simonwa2/F3X-Timing-System/images/base_unit.jpg

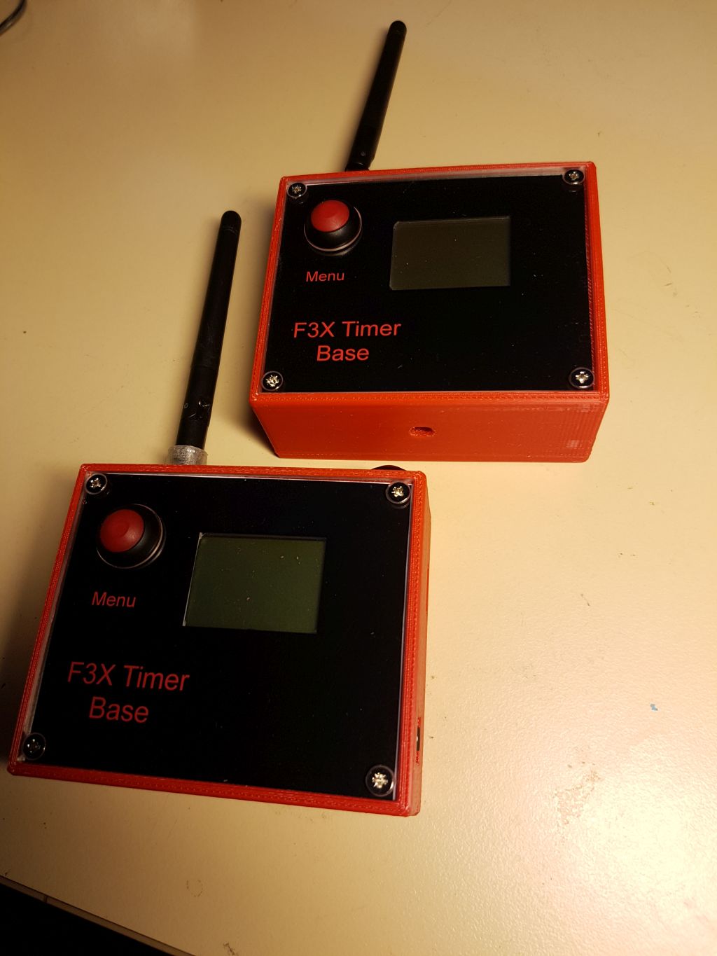
images/base_unit.jpg
