simonwa2/F3X-Timing-System/images/Mini_DIN_6_Connector.jpg

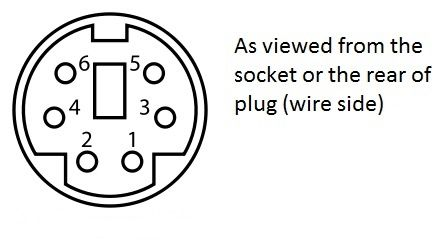
images/Mini_DIN_6_Connector.jpg
