simonwa2/F3X-Timing-System/images/picam_batteries.jpg

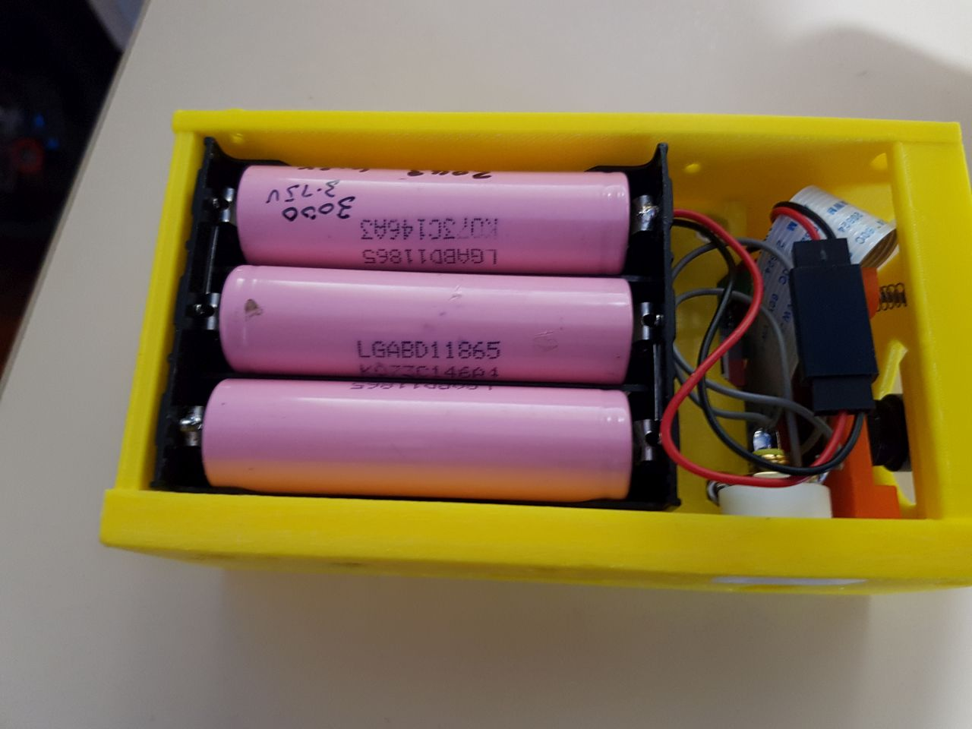
images/picam_batteries.jpg
