simonwa2/F3X-Timing-System/images/picam_bottom.jpg

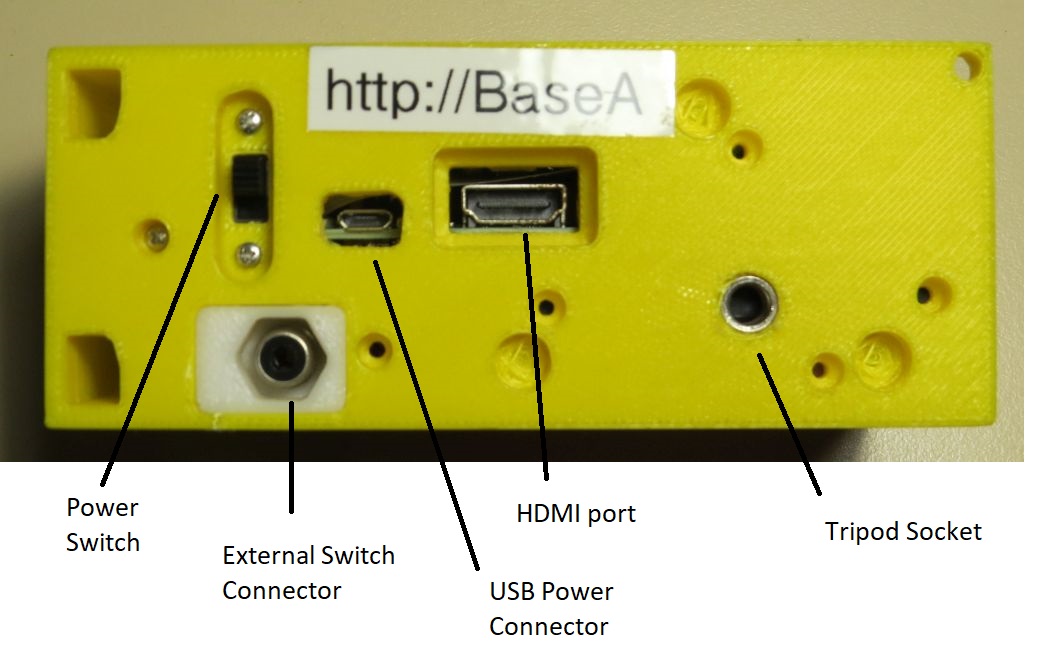
images/picam_bottom.jpg
