simonwa2/F3X-Timing-System/images/picam_preferences.jpg

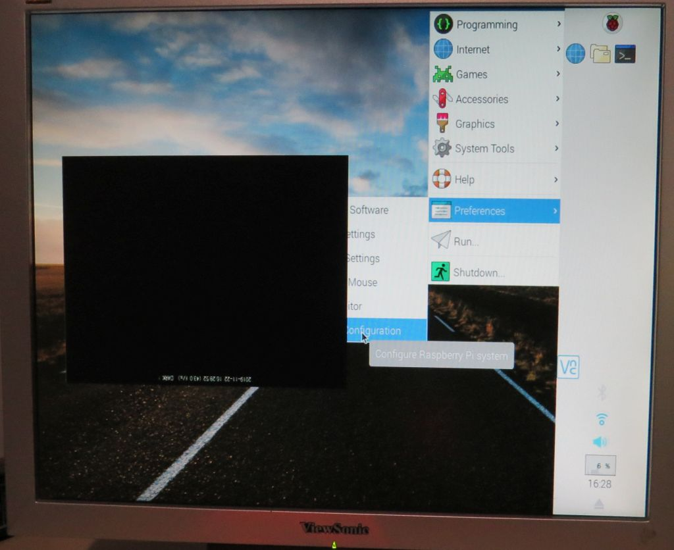
images/picam_preferences.jpg
