simonwa2/F3X-Timing-System/images/Remote.jpg

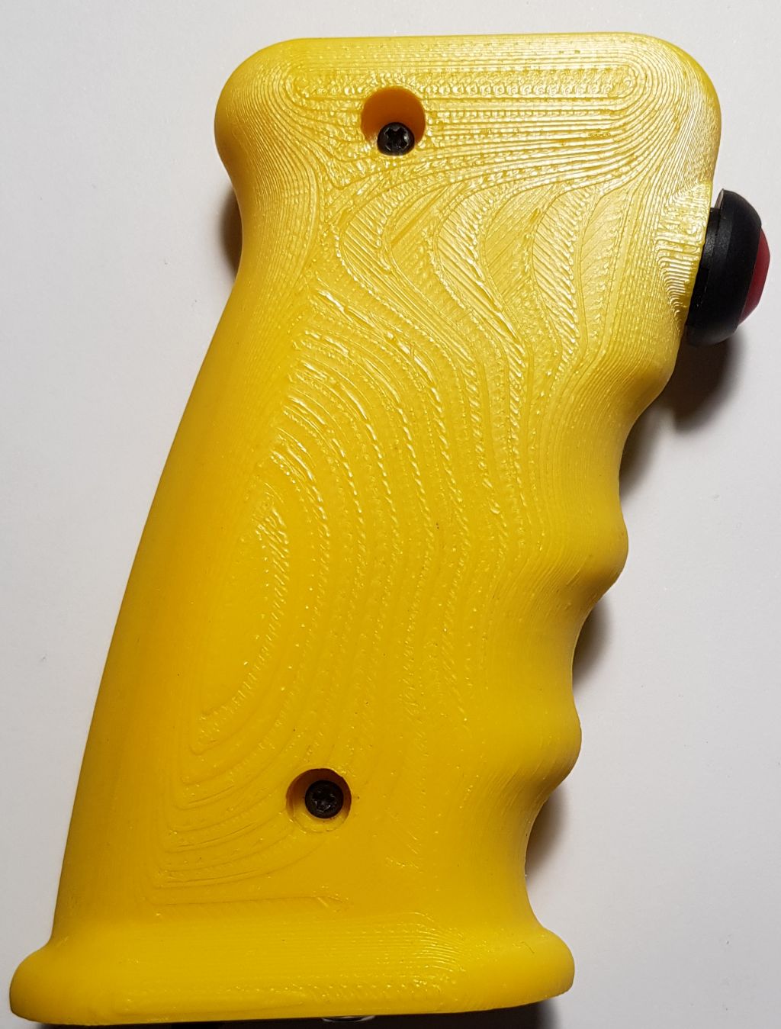
images/Remote.jpg
