simonwa2/F3X-Timing-System/images/timer_v1.JPG

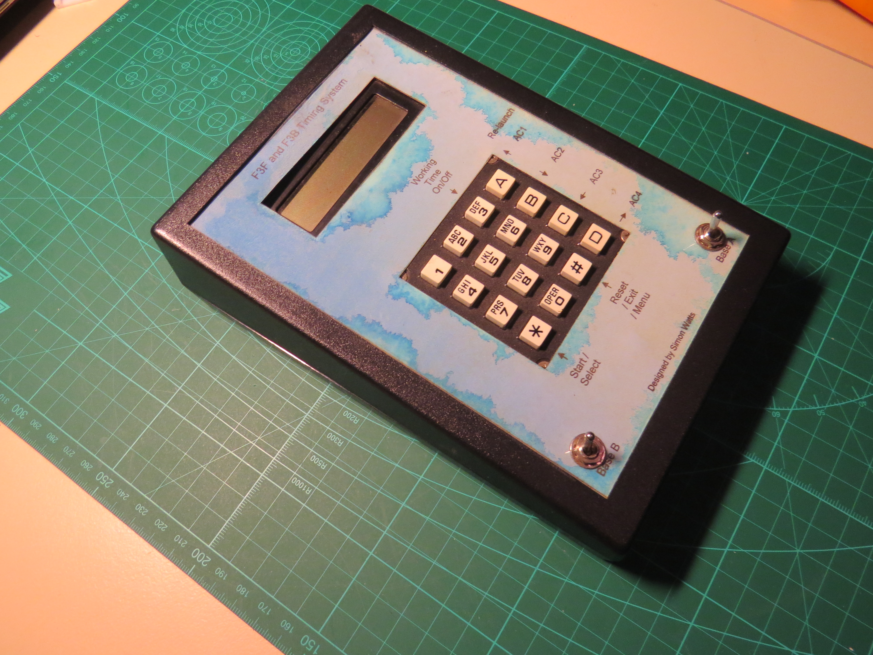
images/timer_v1.JPG
