simonwa2/F3X-Timing-System/images/UniTimer_AP_mode3.png

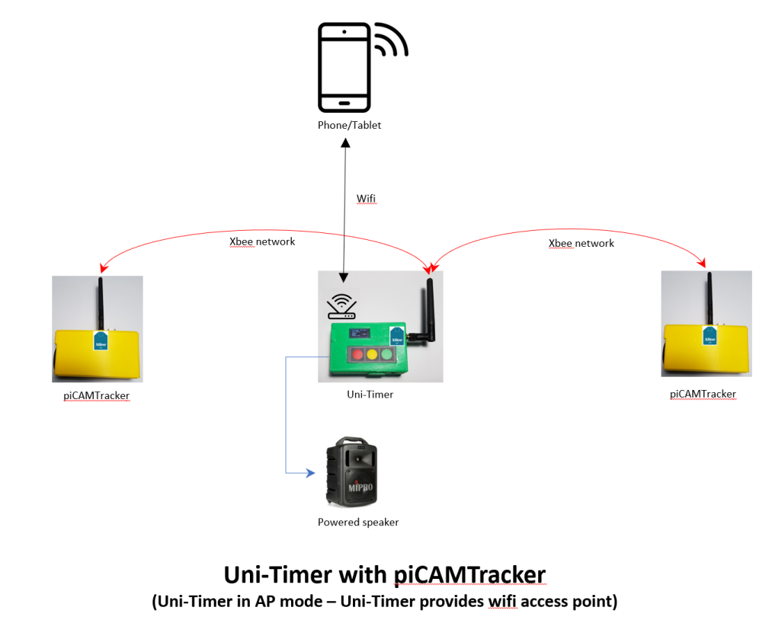
images/UniTimer_AP_mode3.png
