simonwa2/F3X-Timing-System/images/UniTimer_no_wifi1.png

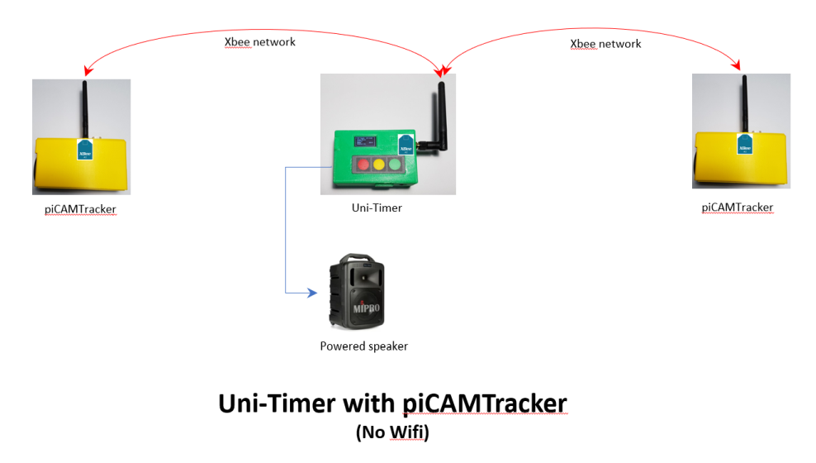
images/UniTimer_no_wifi1.png
